243-510-MA/243-510-A16/Documentation/Schemas/Module capteur/Module Porte/Branchement Module Porte.jpg

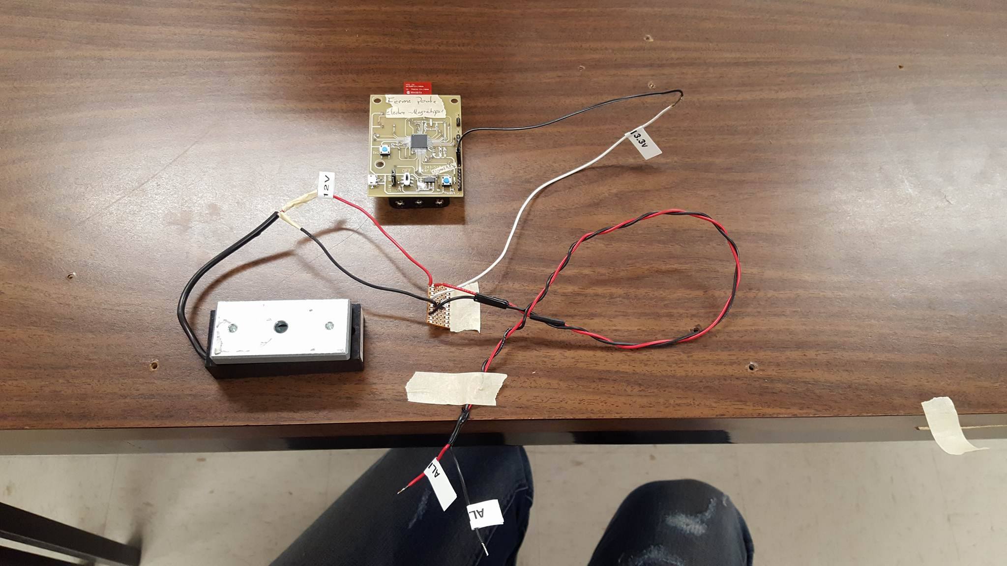
Documentation/Schemas/Module capteur/Module Porte/Branchement Module Porte.jpg
