243-510-MA/243-510-A16/Documentation/Microchip/84713D Gain.png

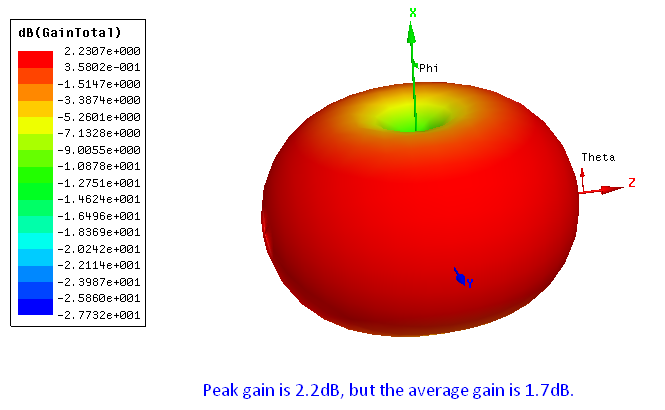
Documentation/Microchip/84713D Gain.png
