243-510-MA/243-510-A16/MASTER/Exemple Miwi/v2015_08_10/framework/driver/touch_screen/src/drv_touch_resistive_adc.c

/*******************************************************************************
 Simple 4-Wire Resistive Touch Screen Driver for the Microchip Graphics Library

  Company:
    Microchip Technology Inc.

  File Name:
    drv_touch_resistive_adc.c

  Summary:
    This module implements the driver for the 4-simple wire resistive
    touch screen.
*******************************************************************************/

// DOM-IGNORE-BEGIN
/*******************************************************************************
Copyright (c) 2013 released Microchip Technology Inc.  All rights reserved.

Microchip licenses to you the right to use, modify, copy and distribute
Software only when embedded on a Microchip microcontroller or digital signal
controller that is integrated into your product or third party product
(pursuant to the sublicense terms in the accompanying license agreement).

You should refer to the license agreement accompanying this Software for
additional information regarding your rights and obligations.

SOFTWARE AND DOCUMENTATION ARE PROVIDED "AS IS" WITHOUT WARRANTY OF ANY KIND,
EITHER EXPRESS OR IMPLIED, INCLUDING WITHOUT LIMITATION, ANY WARRANTY OF
MERCHANTABILITY, TITLE, NON-INFRINGEMENT AND FITNESS FOR A PARTICULAR PURPOSE.
IN NO EVENT SHALL MICROCHIP OR ITS LICENSORS BE LIABLE OR OBLIGATED UNDER
CONTRACT, NEGLIGENCE, STRICT LIABILITY, CONTRIBUTION, BREACH OF WARRANTY, OR
OTHER LEGAL EQUITABLE THEORY ANY DIRECT OR INDIRECT DAMAGES OR EXPENSES
INCLUDING BUT NOT LIMITED TO ANY INCIDENTAL, SPECIAL, INDIRECT, PUNITIVE OR
CONSEQUENTIAL DAMAGES, LOST PROFITS OR LOST DATA, COST OF PROCUREMENT OF
SUBSTITUTE GOODS, TECHNOLOGY, SERVICES, OR ANY CLAIMS BY THIRD PARTIES
(INCLUDING BUT NOT LIMITED TO ANY DEFENSE THEREOF), OR OTHER SIMILAR COSTS.
*******************************************************************************/
// DOM-IGNORE-END

#include "system.h"

#include <stdint.h>
#include "gfx/gfx.h"
#include "driver/touch_screen/drv_touch_screen.h"
#include "driver/touch_screen/drv_touch_resistive_adc.h"

// Error checking
#ifndef RESISTIVETOUCH_ADPCFG_YPOS
#error "The macro RESISTIVETOUCH_ADPCFG_YPOS is not defined (analog port pins (ANSx or ADxPCFG)). Define in system_config.h"
#endif
#ifndef RESISTIVETOUCH_ADPCFG_XPOS
#error "The macro RESISTIVETOUCH_ADPCFG_XPOS is not defined (analog port pins (ANSx or ADxPCFG)). Define in system_config.h"
#endif

#ifndef RESISTIVETOUCH_XP_Signal
#error "The macro RESISTIVETOUCH_XP_Signal is not defined (LATx bit). Define in system_config.h"
#endif
#ifndef RESISTIVETOUCH_XM_Signal
#error "The macro RESISTIVETOUCH_XM_Signal is not defined (LATx bit). Define in system_config.h"
#endif
#ifndef RESISTIVETOUCH_XP_Direction
#error "The macro RESISTIVETOUCH_XP_Direction is not defined (TRISx bit). Define in system_config.h"
#endif
#ifndef RESISTIVETOUCH_XM_Direction
#error "The macro RESISTIVETOUCH_XM_Direction is not defined (TRISx bit). Define in system_config.h"
#endif

#ifndef RESISTIVETOUCH_YP_Signal
#error "The macro RESISTIVETOUCH_YP_Signal is not defined (LATx bit). Define in system_config.h"
#endif
#ifndef RESISTIVETOUCH_YM_Signal
#error "The macro RESISTIVETOUCH_YM_Signal is not defined (LATx bit). Define in system_config.h"
#endif
#ifndef RESISTIVETOUCH_YP_Direction
#error "The macro RESISTIVETOUCH_YP_Direction is not defined (TRISx bit). Define in system_config.h"
#endif
#ifndef RESISTIVETOUCH_YM_Direction
#error "The macro RESISTIVETOUCH_YM_Direction is not defined (TRISx bit). Define in system_config.h"
#endif
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
